rokube015/esp32_smart-clock/SW/esp32/components/i2c/i2c_base.cpp

/**
 * @file i2c_base.cpp
 * @brief Implementation of the I2C communication base class for ESP32.
 *
 * This file contains functions to initialize and manage I2C communication using FreeRTOS
 * and ESP-IDF on an ESP32 platform.
 */

#include <cstring>

#include "freertos/FreeRTOS.h"
#include "i2c_base.h"
#include "esp_log.h"

namespace i2c_base{

  /**
   * @brief Constructor for the I2C class.
   * 
   * Initializes the I2C communication with the specified port and mode.
   *
   * @param port The I2C port number.
   * @param mode The I2C mode (master/slave).
   */
  I2C::I2C(i2c_port_num_t port, i2c_mode_t mode){
    esp_log_level_set(I2C_BASE_TAG, ESP_LOG_INFO);
    ESP_LOGI(I2C_BASE_TAG, "set I2C_BASE_TAG log level: %d", ESP_LOG_INFO);

    mport = port;
    mmode = mode;
  }
  /**
   * @brief Destructor for the I2C class.
   * 
   * Deletes the I2C master bus handle when the object is destroyed.
   */
  I2C::~I2C(){
    i2c_del_master_bus(mi2c_bus_handle);
  }
  /**
   * @brief Acquires the I2C port semaphore.
   * 
   * Ensures exclusive access to the I2C port.
   *
   * @return 
   *   - ESP_OK if the semaphore was successfully taken.
   *   - ESP_FAIL if acquiring the semaphore failed.
   */
  esp_err_t I2C::take_i2c_port_semaphore(){
    esp_err_t r = ESP_OK;
    if(xSemaphoreTake(i2c_port_semaphore, pdMS_TO_TICKS(I2C_TIMEOUT)) == pdTRUE){
      r = ESP_OK;
    }
    else{
      ESP_LOGE(I2C_BASE_TAG, "fail to take i2c_port_semaphore.");
      r = ESP_FAIL;
    }
    return r;
  }
  /**
   * @brief Releases the I2C port semaphore.
   * 
   * Allows other tasks to use the I2C port.
   *
   * @return 
   *   - ESP_OK if the semaphore was successfully released.
   *   - ESP_FAIL if releasing the semaphore failed.
   */
  esp_err_t I2C::release_i2c_port_semaphore(){
    esp_err_t r = ESP_OK;
    if(xSemaphoreGive(i2c_port_semaphore) == pdTRUE){
      r = ESP_OK;
    }
    else{
      ESP_LOGE(I2C_BASE_TAG, "fail to release i2c_port_semaphore.");
      r = ESP_FAIL;
    }
    return r; 
  }
  /**
   * @brief Initializes the I2C port.
   * 
   * Sets up the I2C configuration, including master or slave mode.
   *
   * @param pullup_enable Enables internal pull-up resistors if true.
   * @return ESP_OK on success, ESP_FAIL on failure.
   */
  esp_err_t I2C::init(bool pullup_enable){
    esp_err_t r = ESP_OK;
    if(r == ESP_OK){ 
      i2c_port_semaphore = xSemaphoreCreateMutex();
      if(i2c_port_semaphore == NULL){
        ESP_LOGE(I2C_BASE_TAG, "fail to create i2c_port_semaphore.");
      }
    }

    if(r == ESP_OK){
      if(take_i2c_port_semaphore() == ESP_OK){
        if(mmode == I2C_MODE_MASTER){
          mi2c_bus_config.i2c_port = mport;
          mi2c_bus_config.sda_io_num = SDA_PIN;
          mi2c_bus_config.scl_io_num = SCL_PIN;
          mi2c_bus_config.clk_source = I2C_CLK_SRC_DEFAULT;
          mi2c_bus_config.glitch_ignore_cnt = 7;
          mi2c_bus_config.intr_priority = 0;
          mi2c_bus_config.trans_queue_depth = 0; 
          mi2c_bus_config.flags.enable_internal_pullup = pullup_enable;
          mi2c_bus_config.flags.allow_pd = 0;      
          r = i2c_new_master_bus(&mi2c_bus_config, &mi2c_bus_handle);
          if(r != ESP_OK){
            ESP_LOGE(I2C_BASE_TAG, "fail to set i2c port to master mode. error code:%s", esp_err_to_name(r));
          }
        }
        else{
          ESP_LOGE(I2C_BASE_TAG, "fail to set i2c port to slave mode");
        }
        r |= release_i2c_port_semaphore(); 
      }
    }
    return r;
  }

  /**
   * @brief Gets the I2C master bus handle.
   * 
   * @return The I2C master bus handle.
   */ 
  i2c_master_bus_handle_t I2C::get_i2c_master_bus_handle(){
    return mi2c_bus_handle;
  }

  /**
   * @brief Reads a single byte from the I2C device.
   * 
   * @param dev_handle The I2C device handle.
   * @param pcommand Pointer to the command buffer.
   * @param command_size Size of the command buffer.
   * @param pread_data_buffer Pointer to store the read data.
   * @return ESP_OK on success, ESP_FAIL on failure.
   */
  esp_err_t I2C::read_byte(i2c_master_dev_handle_t dev_handle, 
      const uint8_t* pcommand, size_t command_size,
      uint8_t* pread_data_buffer){
    esp_err_t r = ESP_OK;

    if(r == ESP_OK){
      if(take_i2c_port_semaphore() == ESP_OK){ 
        r = i2c_master_transmit_receive(dev_handle, pcommand, command_size, 
            pread_data_buffer, 1, pdMS_TO_TICKS(1000));
        if(r != ESP_OK){
          ESP_LOGE(I2C_BASE_TAG, "fail to read data.");
        }
        r |= release_i2c_port_semaphore(); 
      }
    }
    return r; 
  }

  /**
   * @brief Writes a single byte to the I2C device.
   * 
   * @param dev_handle The I2C device handle.
   * @param pcommand Pointer to the command buffer.
   * @param command_size Size of the command buffer.
   * @param write_data The data byte to write.
   * @return ESP_OK on success, ESP_FAIL on failure.
   */
  esp_err_t I2C::write_byte(i2c_master_dev_handle_t dev_handle, 
      const uint8_t* pcommand, size_t command_size, 
      const uint8_t write_data){
    esp_err_t r = ESP_OK;

    uint8_t* send_buffer = (uint8_t*)malloc(command_size + 1);
    if(send_buffer == NULL){
      r = ESP_FAIL;
      ESP_LOGE(I2C_BASE_TAG, "fail to alloc buffer.");
    }

    if(r == ESP_OK){
      memcpy(send_buffer, pcommand, command_size); 
      memcpy(send_buffer + command_size, &write_data, 1); 
      if(take_i2c_port_semaphore() == ESP_OK){ 
        r = i2c_master_transmit(dev_handle, send_buffer, 2, pdMS_TO_TICKS(I2C_TIMEOUT));
        if(r != ESP_OK){
          ESP_LOGE(I2C_BASE_TAG, "fail to send data.");
        }
        r |= release_i2c_port_semaphore();
      }
    }
    return r;
  }
  /**
   * @brief Reads multiple bytes of data from the I2C device.
   *
   * This function sends a command to the I2C device and reads the specified number of bytes into the provided buffer.
   * It ensures thread safety by acquiring the I2C semaphore before transmission and releasing it afterward.
   *
   * @param[in] dev_handle The I2C device handle.
   * @param[in] pcommand Pointer to the command buffer to be sent before reading data.
   * @param[in] command_size Size of the command buffer.
   * @param[out] pread_data_buffer Pointer to the buffer where the read data will be stored.
   * @param[in] read_buffer_size Number of bytes to read from the I2C device.
   * 
   * @return 
   *   - ESP_OK if data was successfully read.
   *   - ESP_FAIL if there was an error in the read operation.
   */ 
  esp_err_t I2C::read_data(i2c_master_dev_handle_t dev_handle, 
      const uint8_t* pcommand, size_t command_size, 
      uint8_t* pread_data_buffer, size_t read_buffer_size){
    esp_err_t r = ESP_OK;

    if(r == ESP_OK){
      if(take_i2c_port_semaphore() == ESP_OK){ 
        r = i2c_master_transmit_receive(dev_handle, pcommand, command_size, pread_data_buffer, read_buffer_size, pdMS_TO_TICKS(I2C_TIMEOUT));
        if(r != ESP_OK){
          ESP_LOGE(I2C_BASE_TAG, "fail to read data. I2C Error:%s", esp_err_to_name(r));
        }
        r |= release_i2c_port_semaphore();
      }
    }
    return r;
  }

  /**
   * @brief Writes multiple bytes of data to the I2C device.
   *
   * This function sends a command followed by data to an I2C device.
   * It ensures thread safety by acquiring the I2C semaphore before transmission and releasing it afterward.
   *
   * @param[in] dev_handle The I2C device handle.
   * @param[in] pcommand Pointer to the command buffer to be sent before the data.
   * @param[in] command_size Size of the command buffer.
   * @param[in] pwrite_data_buffer Pointer to the buffer containing the data to be written.
   * @param[in] buffer_size Number of bytes to write after the command.
   * 
   * @return 
   *   - ESP_OK if data was successfully written.
   *   - ESP_FAIL if there was an error in the write operation.
   */
  esp_err_t I2C::write_data(i2c_master_dev_handle_t dev_handle, 
      const uint8_t* pcommand, size_t command_size, 
      const uint8_t* pwrite_data_buffer, size_t buffer_size){
    esp_err_t r = ESP_OK;

    size_t send_buffer_size = command_size + buffer_size;
    uint8_t* send_buffer = (uint8_t*) malloc(send_buffer_size);
    if(send_buffer == NULL){
      r = ESP_FAIL;
      ESP_LOGE(I2C_BASE_TAG, "fail to alloc buffer");
    }

    if(r == ESP_OK){
      memcpy(send_buffer, pcommand, command_size); 
      if(buffer_size != 0){
        memcpy(send_buffer + command_size, pwrite_data_buffer, buffer_size);
      } 
      if(take_i2c_port_semaphore() == ESP_OK){ 
        r = i2c_master_transmit(dev_handle, send_buffer, send_buffer_size, pdMS_TO_TICKS(I2C_TIMEOUT));
        if(r != ESP_OK){
          ESP_LOGE(I2C_BASE_TAG, "fail to send data.");
        }
        r |= release_i2c_port_semaphore();
      } 
    }
    free(send_buffer);
    return r;
  }
}
